LokiMetaSmith/Corkscrew-Filter/render_cfd.scad

include <corkscrew.scad>
