LokiMetaSmith/Corkscrew-Filter/configs/filter_holder.scad

include <../config.scad>
part_to_generate = "filter_holder";
include <../corkscrew.scad>
