LokiMetaSmith/Corkscrew-Filter/configs/flat_end_screw.scad

include <../config.scad>
part_to_generate = "flat_end_screw";
include <../corkscrew.scad>
