LokiMetaSmith/Corkscrew-Filter/configs/hex_array_filter.scad

include <../config.scad>
part_to_generate = "hex_array_filter";
include <../corkscrew.scad>
