LokiMetaSmith/Corkscrew-Filter/configs/hose_adapter_cap.scad

include <../config.scad>
part_to_generate = "hose_adapter_cap";
include <../corkscrew.scad>
