LokiMetaSmith/Corkscrew-Filter/configs/modular_filter_assembly.scad

part_to_generate = "modular_filter_assembly";
include <../corkscrew.scad>
