LokiMetaSmith/Corkscrew-Filter/configs/single_cell_filter.scad

include <../config.scad>
part_to_generate = "single_cell_filter";
include <../corkscrew.scad>
