LokiMetaSmith/Corkscrew-Filter/modules/cutters.scad

// =============================================================================
// --- Cutter Modules ---
// =============================================================================
// This file contains all the modules that are used as "knives" or cutting
// tools to subtract geometry from other parts.

/**
 * Module: SimpleSlitCutter
 * Description: Creates a simple rectangular helical cutting tool for making slits.
 * Arguments: (Same as MultiHelixRamp)
 */
module SimpleSlitCutter(h, twist, dia, helices, offset_angle=ramp_width_degrees/2) {
    // Overlap epsilon to ensure clean cuts (Epsilon Rule for Manifold Geometry)
    eps = 0.05;
    for (i = [0 : helices - 1]) {
        rotate([0, 0, i * (360 / helices) + offset_angle])
        linear_extrude(height = h + eps, twist = twist, center = true, slices = h > 0 ? h * 2 : 1)
            // Shift outward by eps/2 and increase width by eps
            translate([dia / 2 - slit_depth_mm / 2 + eps/2, 0])
                square([slit_depth_mm + eps, slit_width_mm], center = true);
    }
}

/**
 * Module: RampedSlitKnife
 * Description: Creates a more complex cutting tool for making slits with a ramped lead-in.
 * Arguments: (Same as MultiHelixRamp)
 */
module RampedSlitKnife(h, twist, dia, helices, offset_angle=ramp_width_degrees/2) {
    twist_per_mm = twist / h;
    ramp_len = slit_ramp_length_mm;
    open_len = slit_open_length_mm;
    eps = 0.05; // Overlap epsilon to ensure clean cuts

    for (i = [0 : helices - 1]) {
        rotate([0, 0, i * (360 / helices) + offset_angle]) {
            translate([0, 0, -h/2 - eps/2]) { // extend downward
                union() {
                    // 1. The Ramp using hull (interpolates between start surface and full depth)
                    hull() {
                        // Bottom slice: A thin rectangle at dia/2 (surface), depth ~0
                        // Extend outward by eps
                        translate([0,0,0])
                        rotate([0,0,0])
                        translate([dia/2, 0])
                        translate([-0.01, -slit_width_mm/2]) // Depth 0.01
                            cube([0.01 + eps, slit_width_mm, 0.01]);

                        // Top slice: A rectangle at dia/2 - depth, depth full
                        // Extend outward by eps
                        translate([0,0,ramp_len])
                        rotate([0,0,twist_per_mm * ramp_len])
                        translate([dia/2 - slit_depth_mm, -slit_width_mm/2, -0.01])
                            cube([slit_depth_mm + eps, slit_width_mm, 0.01]);
                    }

                    // 2. The Body (Open Slit)
                     translate([0,0,ramp_len - 0.01]) // overlap with hull
                     rotate([0, 0, twist_per_mm * ramp_len])
                     linear_extrude(height = open_len + eps, twist = twist_per_mm * open_len, center=false) {
                         translate([dia/2 - slit_depth_mm, -slit_width_mm/2])
                             square([slit_depth_mm + eps, slit_width_mm]);
                     }
                }
            }
        }
    }
}

/**
 * Module: RampedKnifeShape
 * Description: Helper module to create a single knife with a chamfered leading edge.
 */
module RampedKnifeShape(h, twist, radius, profile_radius) {
    chamfer_h = slit_chamfer_height;
    body_h = h - chamfer_h;
    twist_per_mm = h > 0 ? twist / h : 0;
    chamfer_twist = twist_per_mm * chamfer_h;
    body_twist = twist_per_mm * body_h;

    // Define the 2D profile polygon dimensions
    w = profile_radius * 2;

    // Calculate points for the chamfer polyhedron
    // Bottom points: Scaled by 0.5, at Z=0, translated by radius
    // Top points: Full scale, at Z=chamfer_h, translated by radius, rotated by chamfer_twist

    // Bottom Polygon (Scaled 0.5)
    // Original: [0,0], [w, -w], [w, w]
    // Scaled: [0,0], [0.5w, -0.5w], [0.5w, 0.5w]
    // Translated by [radius, 0]: [radius, 0], [radius+0.5w, -0.5w], [radius+0.5w, 0.5w]
    p0 = [radius, 0, 0];
    p1 = [radius + 0.5*w, -0.5*w, 0];
    p2 = [radius + 0.5*w, 0.5*w, 0];

    // Top Polygon (Full size)
    // Translated by [radius, 0]: [radius, 0], [radius+w, -w], [radius+w, w]
    // Then Rotated by chamfer_twist
    ct_rad = chamfer_twist;

    // Function to rotate point around Z
    function rotZ(p, angle) = [
        p[0]*cos(angle) - p[1]*sin(angle),
        p[0]*sin(angle) + p[1]*cos(angle),
        p[2] + chamfer_h
    ];

    p3 = rotZ([radius, 0, 0], ct_rad);
    p4 = rotZ([radius + w, -w, 0], ct_rad);
    p5 = rotZ([radius + w, w, 0], ct_rad);

    eps = 0.05; // Extend out to make sure cuts don't hit manifold boundaries
    chamfer_points = [p0, p1, p2, p3, p4, p5];
    chamfer_faces = [
        [0, 2, 1], // Bottom
        [3, 5, 4], // Top (Reordered to be CW when viewed from outside)
        // Side 1 (Triangulated for planarity)
        [0, 1, 4], [0, 4, 3],
        // Side 2
        [1, 2, 5], [1, 5, 4],
        // Side 3
        [2, 0, 3], [2, 3, 5]
    ];

    // Shift to match center=true of original linear_extrude
    translate([0, 0, -h/2 - eps/2]) {
        union() {
            // Chamfer Section (Polyhedron) extended down
            translate([0,0, -eps])
            polyhedron(points = chamfer_points, faces = chamfer_faces);

            // Main Body Section - Standard helical extrusion
            // Using shifted points to avoid translate() inside linear_extrude which causes issues in WASM
            translate([0, 0, chamfer_h - 0.01])
            rotate([0, 0, chamfer_twist])
            linear_extrude(height = body_h + eps, twist = body_twist, center = false)
                 polygon(points = [[radius - eps, 0], [radius+w+eps, -w-eps], [radius+w+eps, 0], [radius+w+eps, w+eps]]);
        }
    }
}

/**
 * Module: CorkscrewSlitKnife
 * Description: Creates cutting tools to separate bins on the `FlatEndScrew` model.
 * Arguments: (Same as FlatEndScrew)
 */
module CorkscrewSlitKnife(twist, depth, num_bins) {
    pitch_mm = twist == 0 ? 1e9 : depth / (twist / 360);
    de = depth / num_bins;
    yrot = 360 * (1 / pitch_mm) * de;

    for (i = [1:num_bins-1]) {
        j = -num_bins/2 + i;
        rotate([0, 0, -yrot * j])
        translate([0, 0, j * de])
            // Added 0.02 epsilon to length for clean cuts
            RampedKnifeShape(slit_axial_length_mm + 0.02, twist / depth * (slit_axial_length_mm + 0.02), helix_path_radius_mm, helix_profile_radius_mm);
    }
}

// --- Debris Exit Channel Cutters (from corkscrew_filter_v22.scad) ---

/**
 * Module: HelicalChannelCutter
 * Description: Creates a single helical cutting tool that extends radially outward from a cell.
 * Arguments: (Same as MultiHelixRamp)
 */
module HelicalChannelCutter(h, twist, dia, helices) {
    eps = 0.05;
    for (i = [0 : helices - 1]) {
        rotate([0, 0, i * (360 / helices) + ramp_width_degrees/2]) {
            linear_extrude(height = h + eps, twist = twist, center=true, slices = h > 0 ? h*2:1) {
                // This cutter starts at the ramp's outer edge and extends far outwards
                // to cut through the hex array frame.
                translate([dia - eps, 0, 0]) {
                    square([dia*2 + eps, slit_width_mm], center=true);
                }
            }
        }
    }
}

/**
 * Module: StagedExitChannelCutter
 * Description: Creates staged helical channels that match the filter core stages.
 * Arguments: (Same as StagedHelicalStructure)
 */
module StagedExitChannelCutter(total_h, dia, helices, stages) {
    stage_defs = [ [[0, 0.85]], [[0, 0.35], [0.45, 0.85]], [[0, 0.25], [0.30, 0.58], [0.63, 0.92]] ];
    stages_to_build = stage_defs[stages-1];

    for (stage = stages_to_build) {
        start_z_frac = stage[0];
        end_z_frac = stage[1];
        stage_h = (end_z_frac - start_z_frac) * total_h;
        center_z = (start_z_frac + end_z_frac) / 2 * total_h - total_h / 2;
        revolutions = total_revolutions * (stage_h / total_h);
        twist = 360 * revolutions;

        translate([0,0,center_z]) {
            HelicalChannelCutter(stage_h, twist, dia, helices);
        }
    }
}
