LokiMetaSmith/Corkscrew-Filter/modules/primitives.scad

// =============================================================================
// --- Primitive Modules ---
// =============================================================================
// This file contains basic, reusable primitive shapes and tools.

// --- O-Ring Primitives (from corkscrew_filter_v40.scad) ---

/**
 * Module: OringGroove_OD_Cutter
 * Description: Creates a cutting tool for an O-ring groove on an outer cylindrical or flat surface.
 * Arguments:
 * object_dia: The diameter of the object to cut the groove into.
 * oring_cs:   The cross-section diameter of the O-ring.
 * flat:       (boolean) If true, creates a straight cutter for a flat face instead of a toroidal one.
 */
module OringGroove_OD_Cutter(object_dia, oring_cs, flat = false) {
    groove_depth = oring_cs * 0.8;
    groove_width = oring_cs * 1.1;
    cutter_dia = object_dia - 2 * groove_depth;
    if (flat) {
        translate([-object_dia / 2, -groove_width / 2, 0])
            cube([object_dia, groove_width, groove_depth]);
    }
    else {
        difference() {
            cylinder(d = object_dia + 0.2, h = groove_width, center = true);
            cylinder(d = cutter_dia, h = groove_width + 0.2, center = true);
        }
    }
}

/**
 * Module: OringVisualizer
 * Description: Renders a torus shape to represent an O-ring for visualization purposes (Outer Diameter).
 * Arguments:
 * object_dia: The diameter of the object the O-ring sits on.
 * oring_cs:   The cross-section diameter of the O-ring.
 */
module OringVisualizer(object_dia, oring_cs) {
    groove_depth = oring_cs * 0.8;
    torus_radius = object_dia / 2 - groove_depth / 2;
    color("IndianRed") rotate_extrude(convexity = 10) translate([torus_radius, 0, 0]) circle(r = oring_cs / 2);
}

/**
 * Module: OringVisualizer_ID
 * Description: Renders a torus shape to represent an O-ring for visualization purposes (Inner Diameter).
 * Arguments:
 * object_id: The inner diameter of the object the O-ring sits in.
 * oring_cs:  The cross-section diameter of the O-ring.
 */
module OringVisualizer_ID(object_id, oring_cs) {
    groove_depth = oring_cs * 0.8;
    torus_radius = object_id / 2 + groove_depth / 2;
    color("IndianRed") rotate_extrude(convexity = 10) translate([torus_radius, 0, 0]) circle(r = oring_cs / 2);
}

/**
 * Module: OringVisualizer_Face
 * Description: Renders a torus shape to represent an O-ring for visualization purposes (Axial/Face Seal).
 * Arguments:
 * groove_center_dia: The diameter of the center of the groove.
 * oring_cs:   The cross-section diameter of the O-ring.
 */
module OringVisualizer_Face(groove_center_dia, oring_cs) {
    color("IndianRed") rotate_extrude(convexity = 10) translate([groove_center_dia / 2, 0, 0]) circle(r = oring_cs / 2);
}

/**
 * Module: OringVisualizer_Linear
 * Description: Renders a cylinder/capsule shape to represent a linear O-ring seal.
 * Arguments:
 * length:     The length of the seal (matches object_dia in OringGroove_OD_Cutter with flat=true).
 * oring_cs:   The cross-section diameter of the O-ring.
 */
module OringVisualizer_Linear(length, oring_cs) {
    groove_depth = oring_cs * 0.8;
    // The cutter is a cube extending from Z=0 to Z=groove_depth.
    // The O-ring sits "in" the groove, centered at half depth?
    // Usually O-rings are compressed. If we visualize it uncompressed, it might stick out.
    // Let's center it at groove_depth / 2, so it's flush with the bottom of the groove
    // but sticks out the top by (cs/2 - groove_depth/2).
    // Center Z = groove_depth / 2.
    color("IndianRed") translate([0, 0, groove_depth / 2]) rotate([0, 90, 0]) cylinder(h = length, d = oring_cs, center = true);
}


/**
 * Module: OringGroove_ID_Cutter
 * Description: Creates a cutting tool for an O-ring groove on an inner cylindrical surface.
 * Arguments:
 * object_id: The inner diameter of the object to cut the groove into.
 * oring_cs:  The cross-section diameter of the O-ring.
 */
module OringGroove_ID_Cutter(object_id, oring_cs) {
    groove_depth = oring_cs * 0.8;
    groove_width = oring_cs * 1.1;
    rotate_extrude(convexity = 10) translate([object_id / 2 + groove_depth / 2, 0, 0]) square([groove_depth, groove_width], center = true);
}

/**
 * Module: OringGroove_Face_Cutter
 * Description: Creates a cutting tool for an O-ring groove on a flat face (Z-axis).
 * Arguments:
 * groove_center_dia: The diameter of the center of the groove.
 * oring_cs:   The cross-section diameter of the O-ring.
 */
module OringGroove_Face_Cutter(groove_center_dia, oring_cs) {
    groove_depth = oring_cs * 0.8;
    groove_width = oring_cs * 1.1;
    rotate_extrude(convexity = 10) translate([groove_center_dia / 2, 0, 0]) square([groove_width, groove_depth], center = true);
}

/**
 * Module: TubeVisualizer
 * Description: Renders a translucent tube for visualization purposes.
 * Arguments:
 * tube_od:   The outer diameter of the tube.
 * tube_wall: The wall thickness of the tube.
 * length:    The length of the tube section to render.
 * center:    (boolean) If true, centers the tube on the Z-axis. Default: true.
 */
module TubeVisualizer(tube_od, tube_wall, length, center=true) {
    color([0.6, 0.8, 1.0, 0.3]) // Light Blue, Translucent
    difference() {
        cylinder(d = tube_od, h = length, center = center);
        cylinder(d = tube_od - 2 * tube_wall, h = length + 1, center = center);
    }
}
